anaveo/SaltScale/Images/HX711_Harness.jpeg

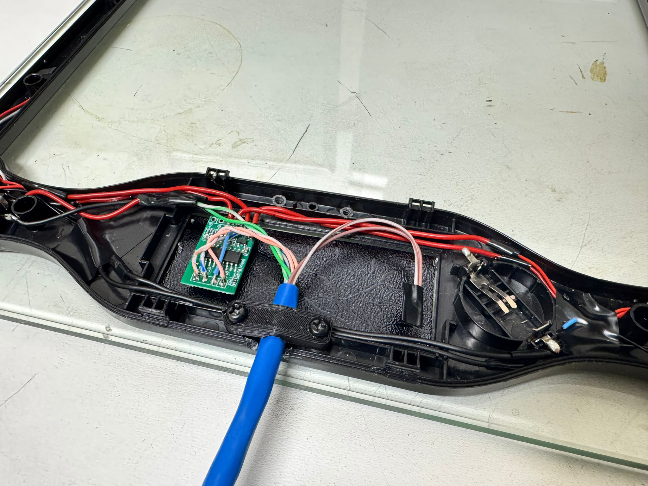
Images/HX711_Harness.jpeg
