anaveo/SaltScale/Images/Monitor_Use.jpeg

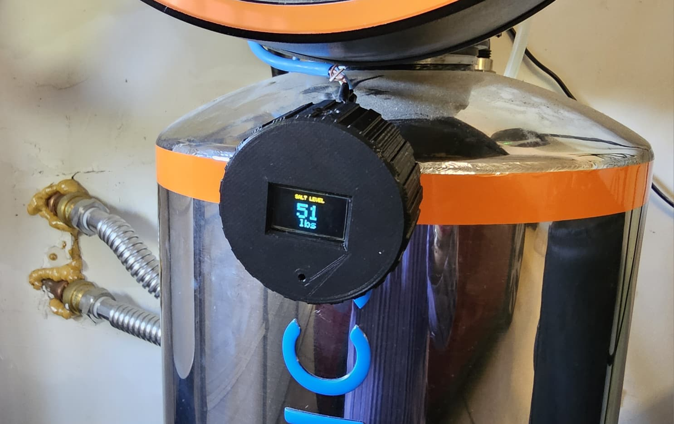
Images/Monitor_Use.jpeg
