anaveo/SaltScale/Images/Monitor_Wired_Harness.jpeg

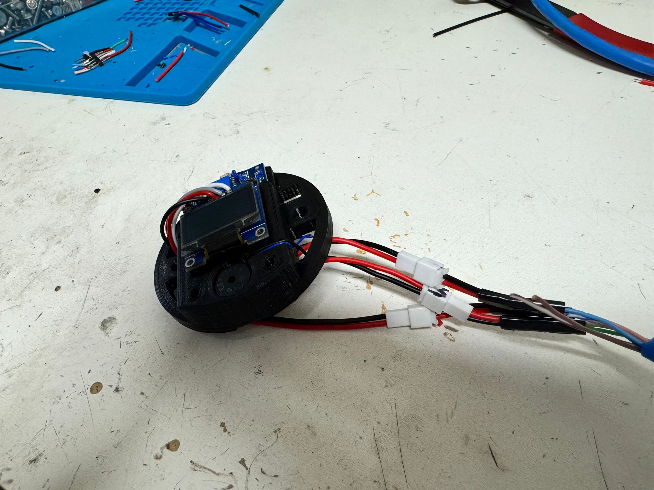
Images/Monitor_Wired_Harness.jpeg
