anaveo/SaltScale/Images/SaltScale_Full_Use.jpeg

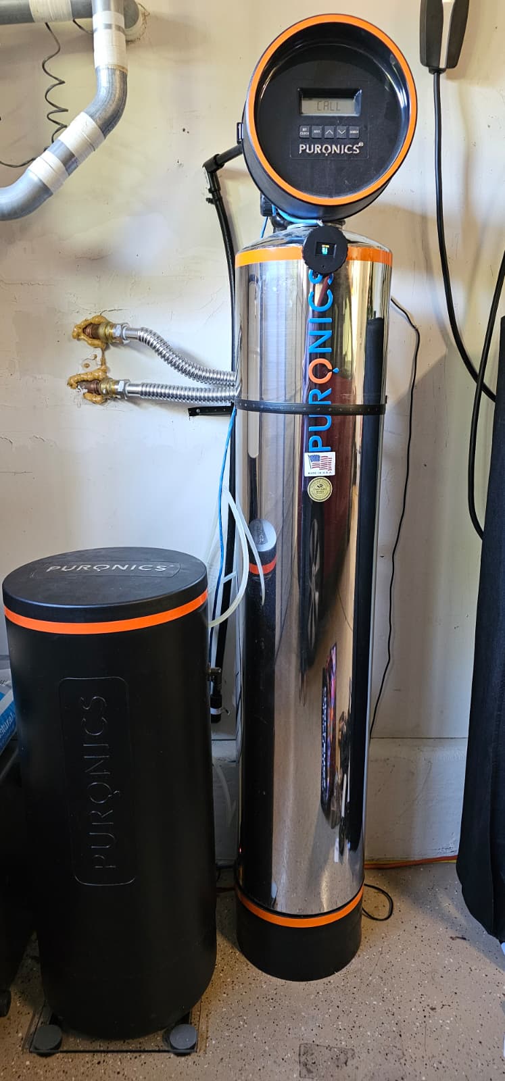
Images/SaltScale_Full_Use.jpeg
