anaveo/SaltScale/Images/Scale_Control_Board.jpeg

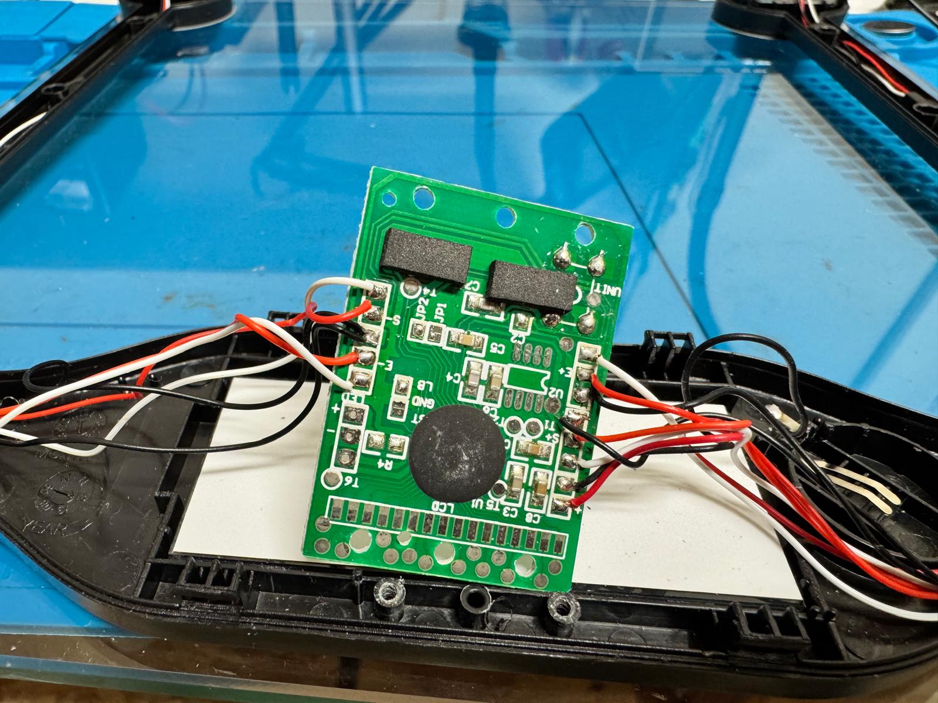
Images/Scale_Control_Board.jpeg
