anaveo/SaltScale/Images/Scale_Open_Back.jpeg

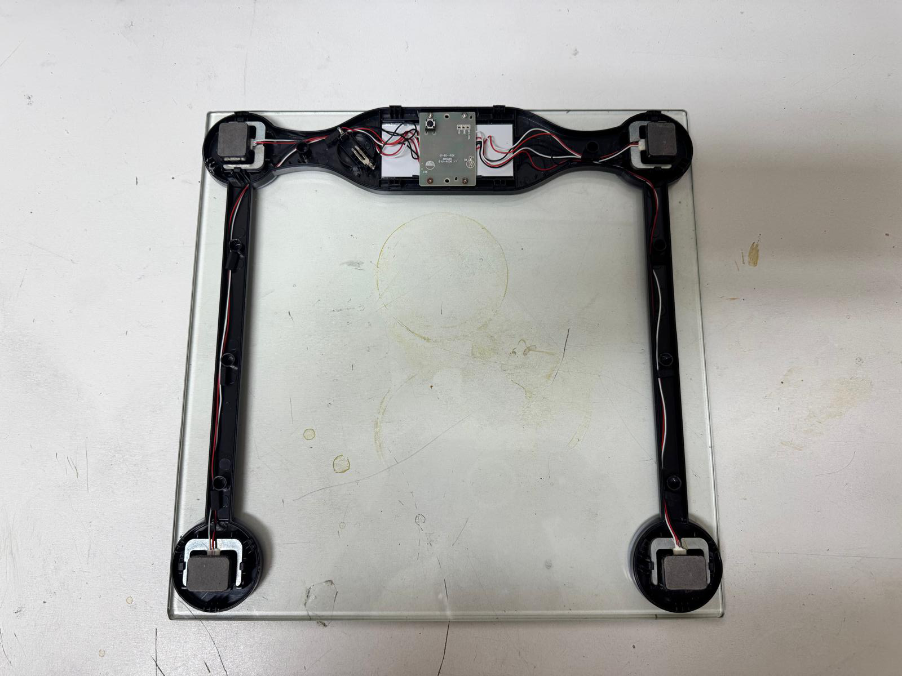
Images/Scale_Open_Back.jpeg
