anaveo/SaltScale/Images/Scale_Sensor.jpeg

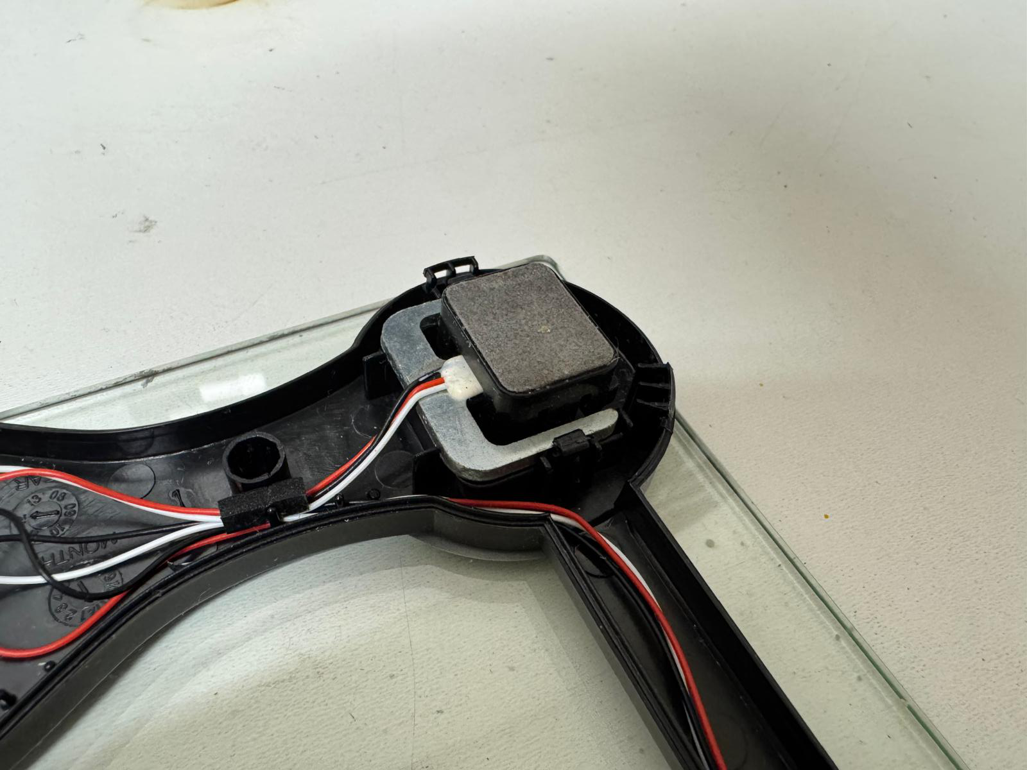
Images/Scale_Sensor.jpeg
