anaveo/SaltScale/Images/Monitor_Parts.jpeg

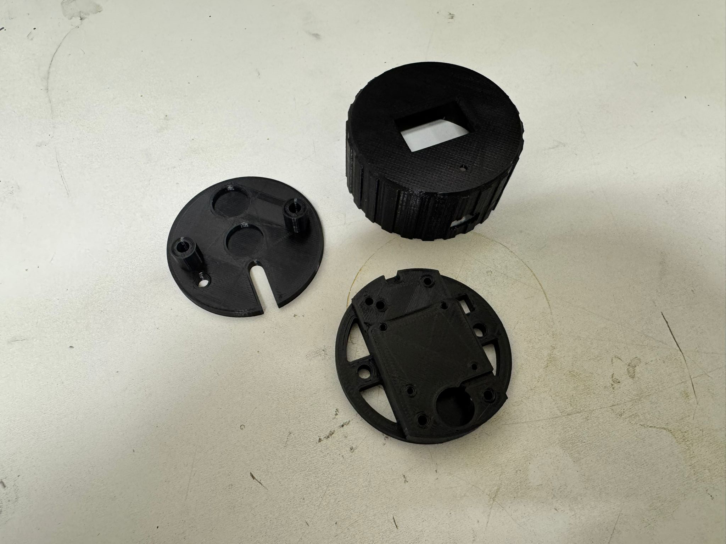
Images/Monitor_Parts.jpeg
