anaveo/SaltScale/Images/HX711_Wiring_Diagram.jpg

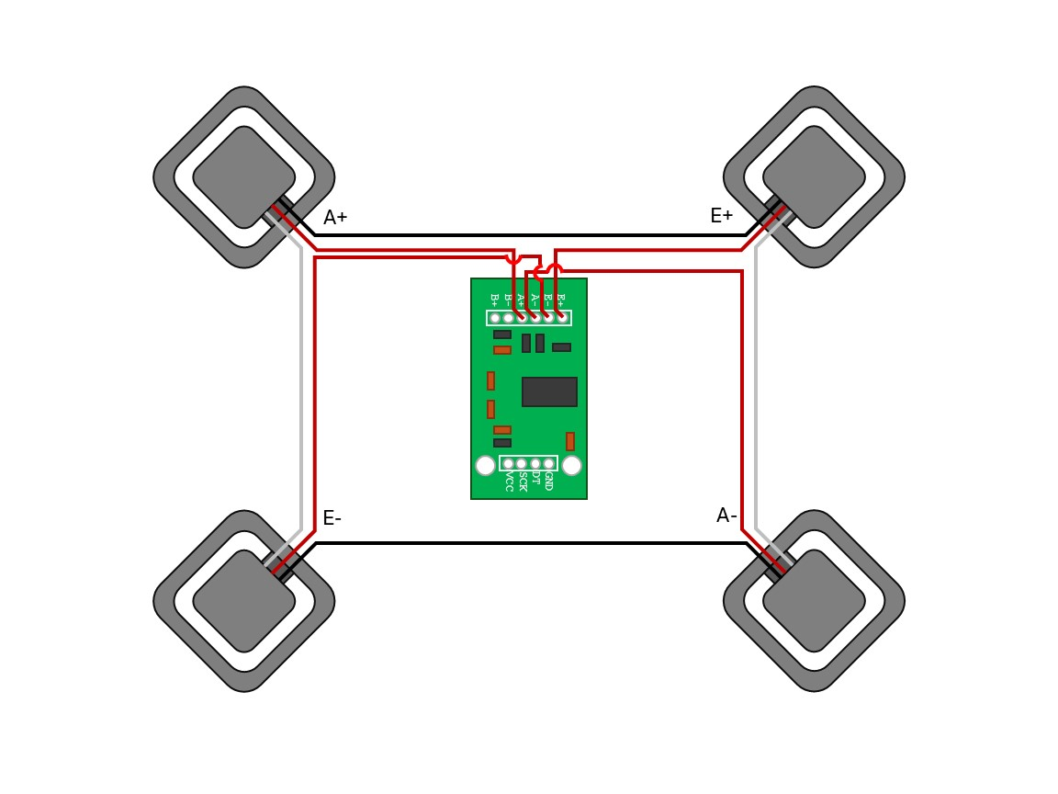
Images/HX711_Wiring_Diagram.jpg
