anaveo/SaltScale/Images/Scale_Assembled.jpeg

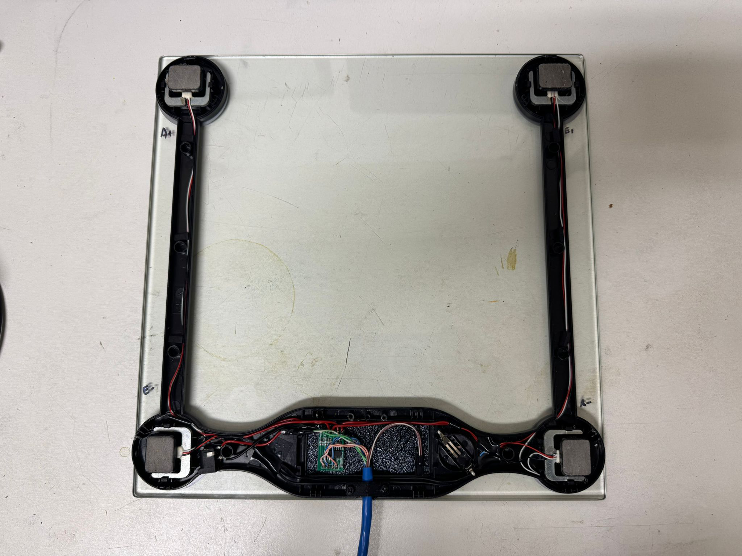
Images/Scale_Assembled.jpeg
