anaveo/SaltScale/Images/Wiring_Diagram.jpg

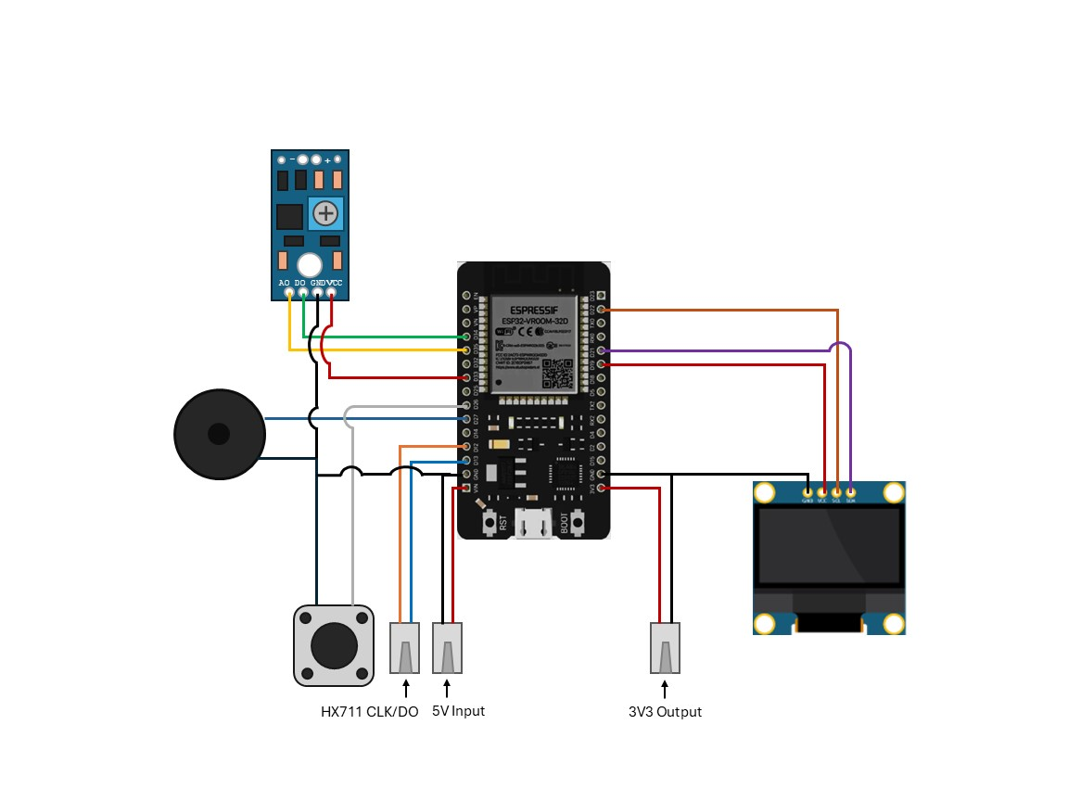
Images/Wiring_Diagram.jpg
