anaveo/SaltScale/Images/Calibration.jpeg

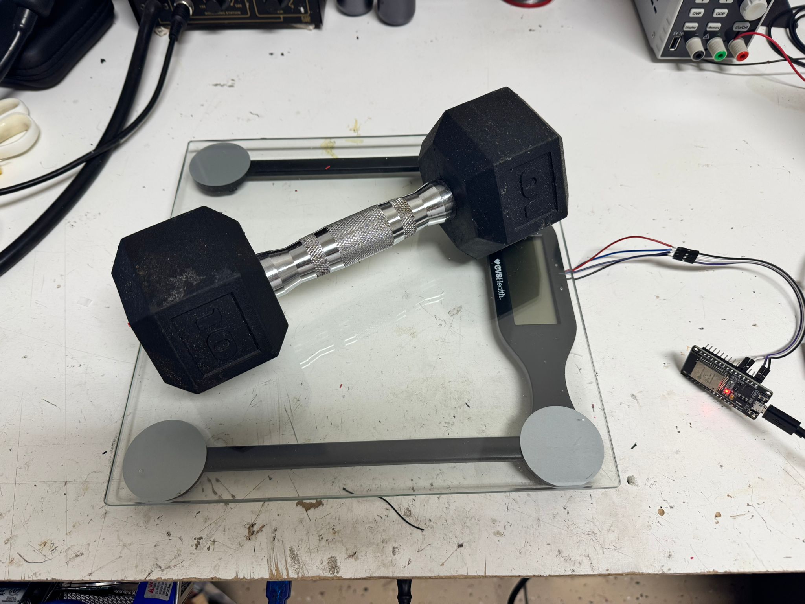
Images/Calibration.jpeg
