anaveo/SaltScale/Images/Scale Calibration.jpeg

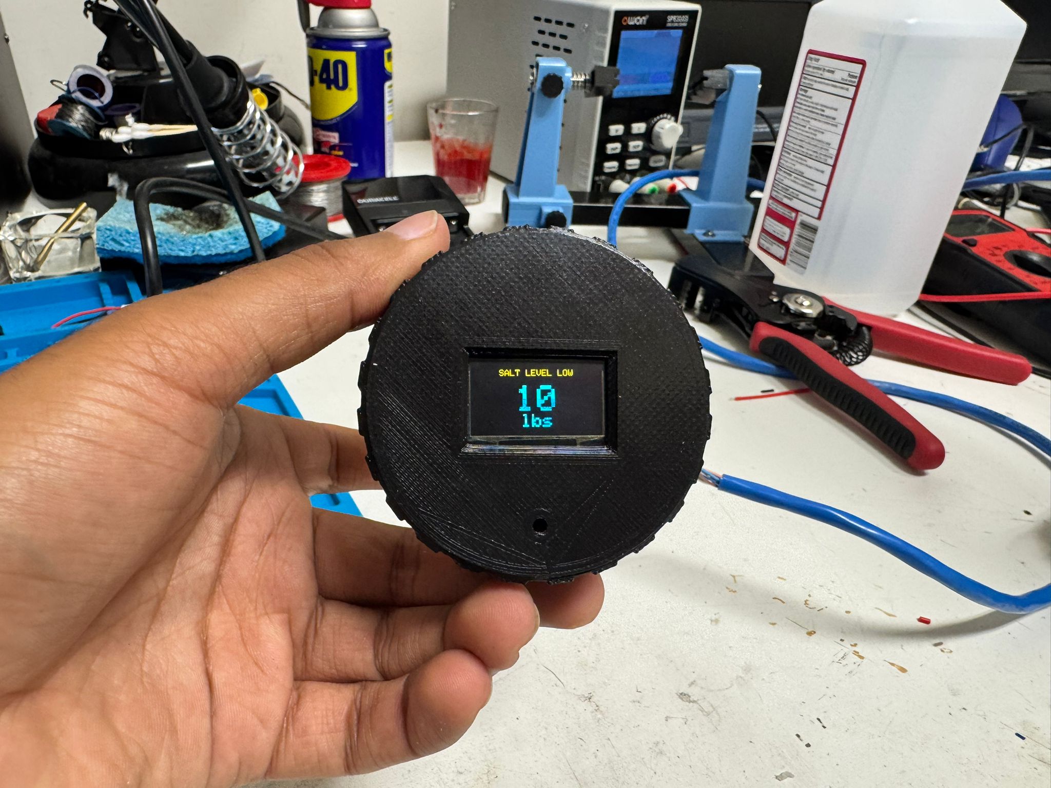
Images/Scale Calibration.jpeg
